topherCantrell/merkuryLEDMatrix/graphic_digits.py

# 10 digts, 0-9, in 3x5 grid format
DIGITS=b'\x01\x01\x01\x01\x00\x01\x01\x00\x01\x01\x00\x01\x01\x01\x01\x00\x00\x01\x00\x00\x01\x00\x00\x01\x00\x00\x01\x00\x00\x01\x01\x01\x01\x00\x00\x01\x01\x01\x01\x01\x00\x00\x01\x01\x01\x01\x01\x01\x00\x00\x01\x01\x01\x01\x00\x00\x01\x01\x01\x01\x01\x00\x01\x01\x00\x01\x01\x01\x01\x00\x00\x01\x00\x00\x01\x01\x01\x01\x01\x00\x00\x01\x01\x01\x00\x00\x01\x01\x01\x01\x01\x01\x01\x01\x00\x00\x01\x01\x01\x01\x00\x01\x01\x01\x01\x01\x01\x01\x00\x00\x01\x00\x00\x01\x00\x00\x01\x00\x00\x01\x01\x01\x01\x01\x00\x01\x01\x01\x01\x01\x00\x01\x01\x01\x01\x01\x01\x01\x01\x00\x01\x01\x01\x01\x00\x00\x01\x01\x01\x01'

def draw_digit(grid, digit, x, y, palette_offset=0):
    """Draw a single digit on the NeoPixels at position (x,y)"""
    grid.draw_image(x, y, 3, 5, DIGITS[digit*15:(digit+1)*15], palette_offset)

def draw_number_centered(grid, number, x, y, palette_offset=0):
    draw_number(grid, number, x - len(str(number)) * 2 + 1, y, palette_offset)

def draw_number(grid, number, x, y, palette_offset=0):
    """Draw a number on the NeoPixels at position (x,y)"""
    digits = str(number)
    for i, digit in enumerate(digits):
        draw_digit(grid, int(digit), x + i * 4, y, palette_offset)
